PubInv/ventmon-ventilator-inline-test-monitor/doc/ethernet_wing.JPG

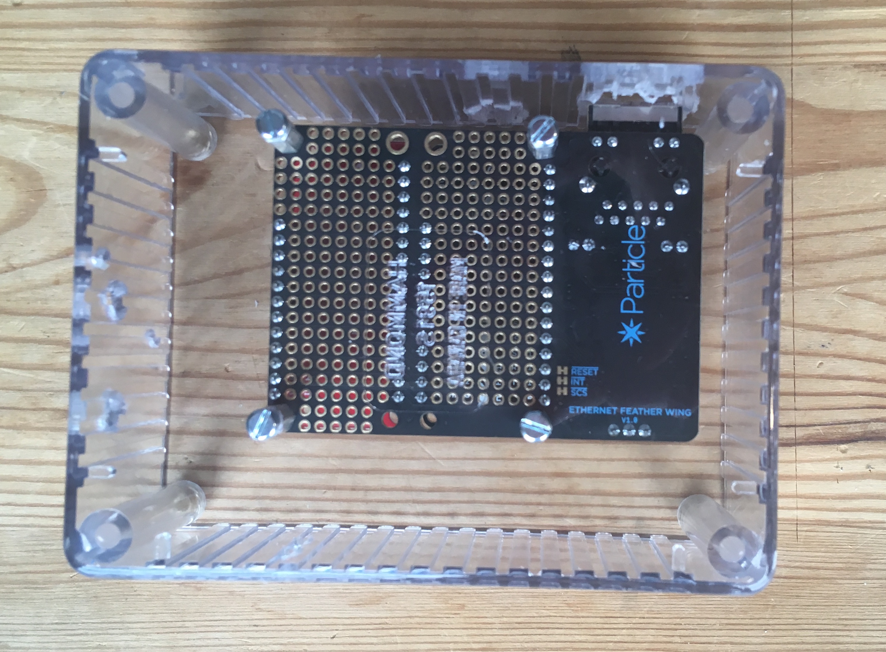
doc/ethernet_wing.JPG
