PubInv/ventmon-ventilator-inline-test-monitor/doc/usb_qwiic.JPG

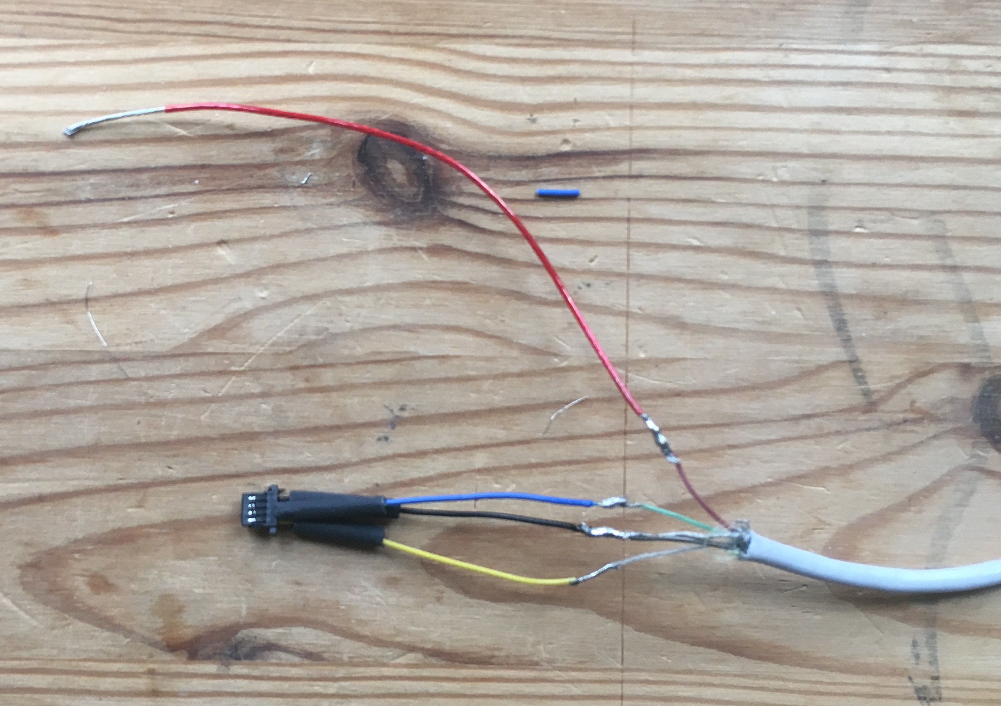
doc/usb_qwiic.JPG
