PubInv/ventmon-ventilator-inline-test-monitor/images/prototype_4.JPG

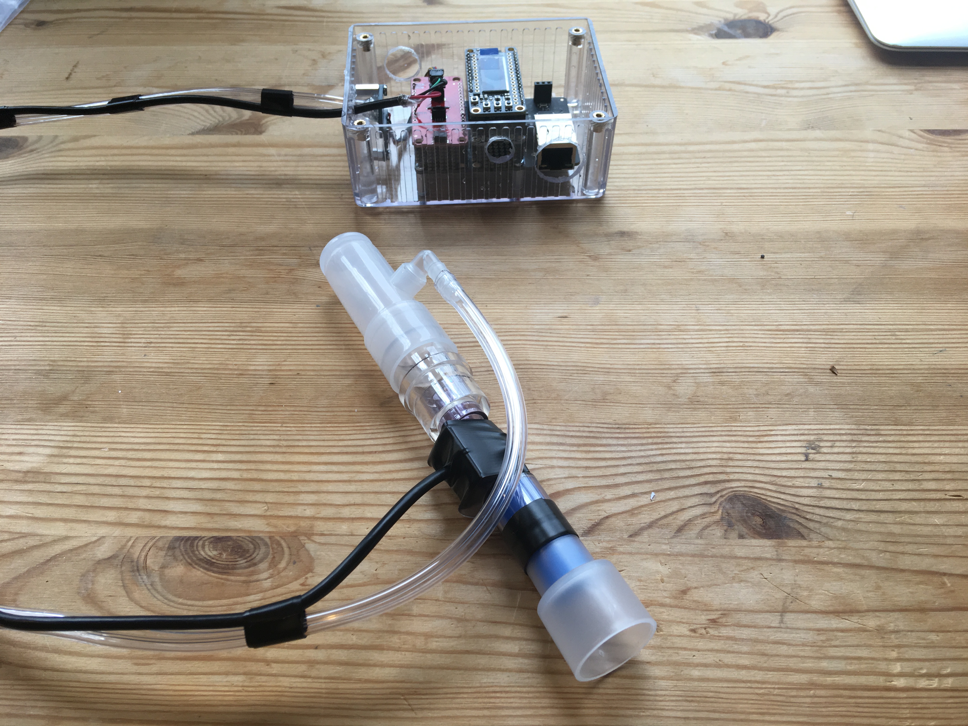
images/prototype_4.JPG
