PubInv/ventmon-ventilator-inline-test-monitor/images/VentMon_OSHWA.png

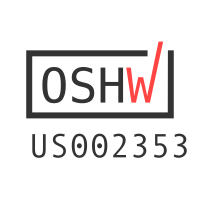
images/VentMon_OSHWA.png
