PubInv/ventmon-ventilator-inline-test-monitor/images/prototype_1.JPG

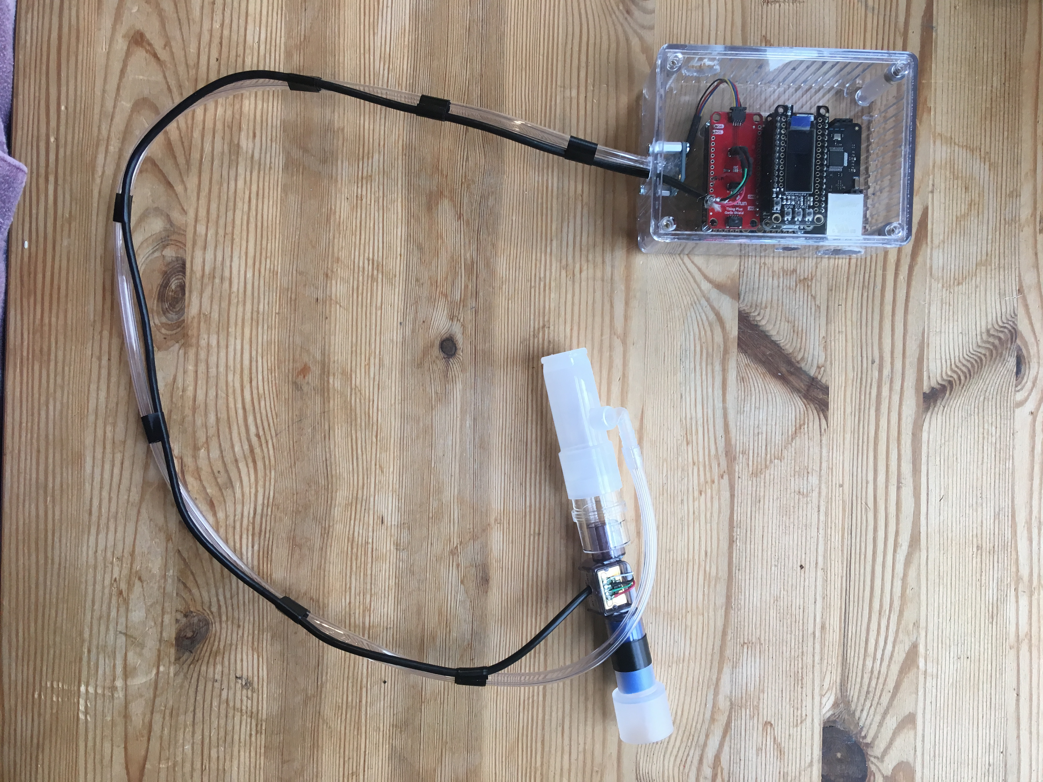
images/prototype_1.JPG
