PubInv/ventmon-ventilator-inline-test-monitor/images/prototype_2.JPG

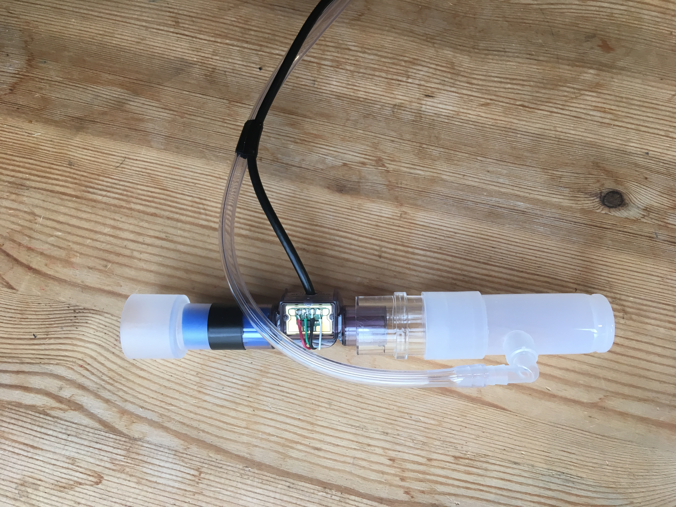
images/prototype_2.JPG
