PubInv/ventmon-ventilator-inline-test-monitor/images/prototype_3.JPG

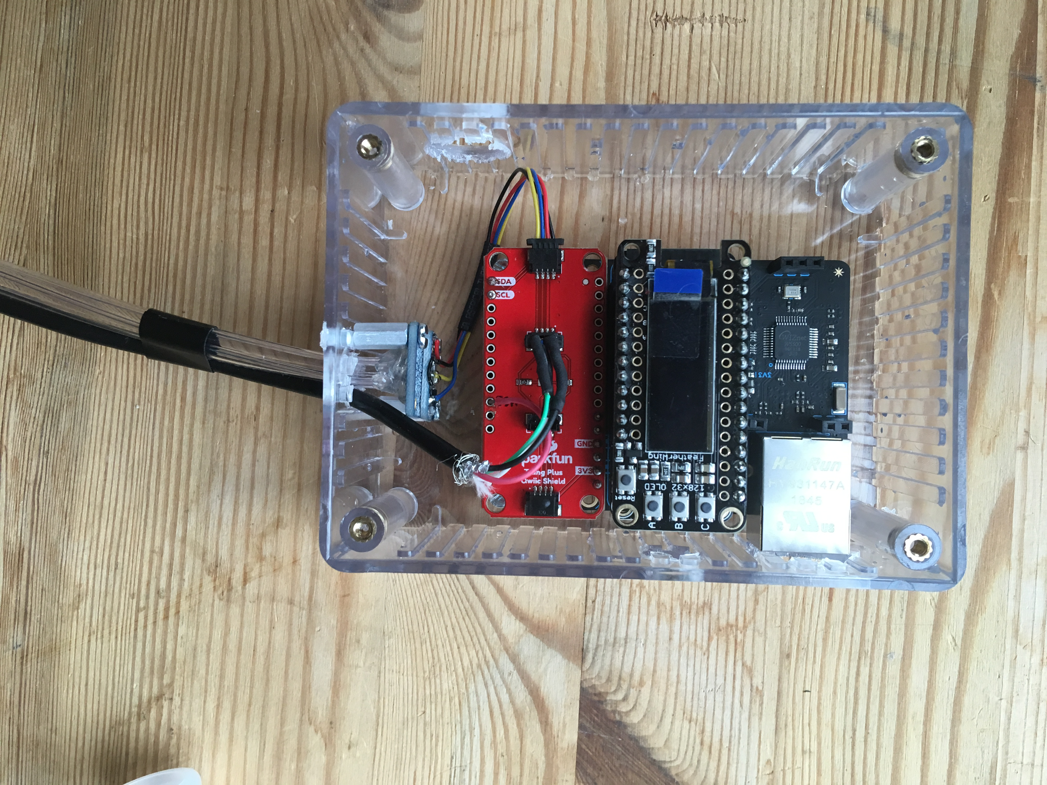
images/prototype_3.JPG
