PubInv/ventmon-ventilator-inline-test-monitor/pi/mounting-bracket-idea/BracketInPlace.JPG

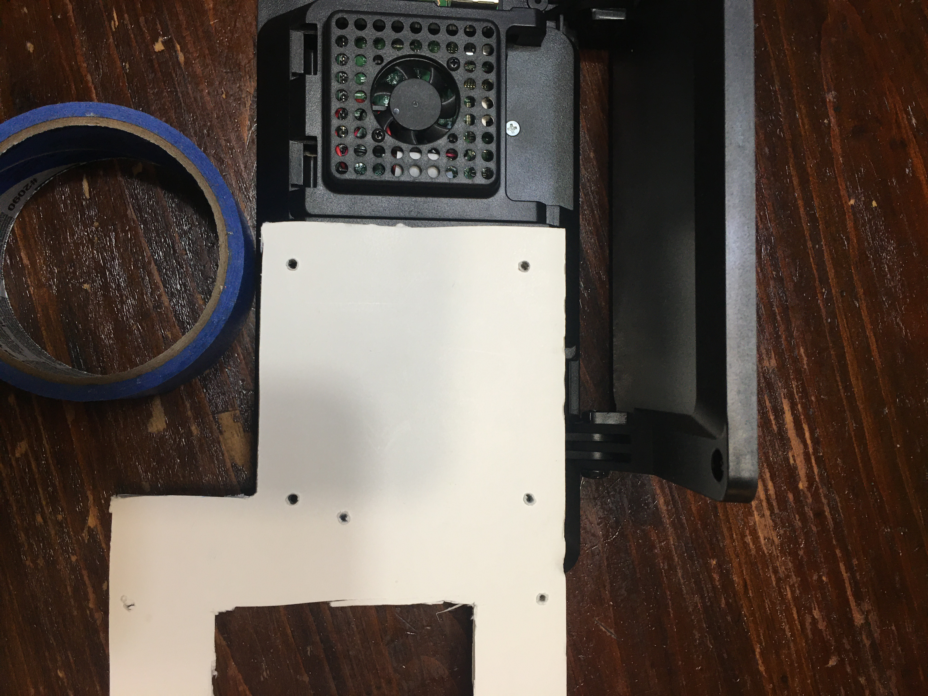
pi/mounting-bracket-idea/BracketInPlace.JPG
